balinth0rvath/AVR-nRF24/sensor/main.cpp

/*
 * sensor.cpp
 *
 * Created: 10/23/2021 3:49:46 PM
 * Author : balinth0horvath
 */ 

#include "common.h"
#include <avr/io.h>
#include "controller.h"

int main(void)
{
/* Replace with your application code */
  Controller controller;  
  controller.runLongLoop();

  while (1) 
  {
  }
}
