balinth0rvath/AVR-nRF24/sensor/include/common.h

/*
 * common.h
 *
 * Created: 10/25/2021 2:41:48 PM
 *  Author: balinth0rvath
 */ 

#ifndef COMMON_H_
#ifndef F_CPU					      // if F_CPU was not defined in Project -> Properties
#define F_CPU 1000000UL			// define it now as 1MHz internal, unsigned long
#endif
#define COMMON_H_

#endif /* COMMON_H_ */
